Derv6464/Magik/test/board_data/vega/filteredDataInfo.csv

ts | filteredAltitudeAGL | filteredAcceleration
-0.75 | 0.8725128173828125 | 0.009731292724609375
-0.74 | 0.4420928955078125 | 0.009731292724609375
-0.73 | 0.4420928955078125 | 0.019464492797851562
-0.72 | 0.4420928955078125 | 0.019464492797851562
-0.71 | 0.4420928955078125 | 0.019464492797851562
-0.7 | 0.4420928955078125 | 0.019464492797851562
-0.69 | 0.4420928955078125 | 0.019464492797851562
-0.68 | 0.5205535888671875 | 0.019464492797851562
-0.67 | 0.5205535888671875 | 0.019464492797851562
-0.66 | 0.5205535888671875 | 0.019464492797851562
-0.65 | 0.5205535888671875 | 0.019464492797851562
-0.64 | 0.946990966796875 | 0.038928985595703125
-0.63 | 1.18878173828125 | 0.05839347839355469
-0.62 | 1.18878173828125 | 0.0486602783203125
-0.61 | 1.013916015625 | 0.0486602783203125
-0.6 | 1.013916015625 | 0.038928985595703125
-0.59 | 1.013916015625 | 0
-0.58 | 1.013916015625 | -0.009731292724609375
-0.57 | 1.1788177490234375 | -0.009731292724609375
-0.56 | 1.1788177490234375 | 0.0486602783203125
-0.55 | 1.1788177490234375 | 0.0486602783203125
-0.54 | 1.013916015625 | 0.0486602783203125
-0.53 | 1.013916015625 | 0.05839347839355469
-0.52 | 0.3279266357421875 | 0
-0.51 | 1.1788177490234375 | 0
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
