Derv6464/Magik/test/board_data/vega/flightInfo.csv

ts | height | velocity | acceleration
-0.75 | 0.4530242681503296 | 0.1455255150794983 | -0.02075336128473282
-0.74 | 0.4542248249053955 | 0.14505557715892792 | -0.02075744792819023
-0.73 | 0.45539671182632446 | 0.14465756714344025 | -0.011028729379177094
-0.72 | 0.45654067397117615 | 0.1442347764968872 | -0.011033594608306885
-0.71 | 0.4576570689678192 | 0.14378778636455536 | -0.01103883609175682
-0.7 | 0.4587462246417999 | 0.14331720769405365 | -0.011044444516301155
-0.69 | 0.45980846881866455 | 0.14282359182834625 | -0.011050410568714142
-0.68 | 0.46245095133781433 | 0.1439698040485382 | -0.011030841618776321
-0.67 | 0.46505051851272583 | 0.1450599730014801 | -0.01101214811205864
-0.66 | 0.4676075279712677 | 0.14609502255916595 | -0.010994315147399902
-0.65 | 0.4701223075389862 | 0.1470758467912674 | -0.010977329686284065
-0.64 | 0.4813291132450104 | 0.1572326123714447 | 0.008643997833132744
-0.63 | 0.497358500957489 | 0.17246860265731812 | 0.02834136039018631
-0.62 | 0.5132084488868713 | 0.1872667670249939 | 0.01883569173514843
-0.61 | 0.5252976417541504 | 0.19802352786064148 | 0.019000258296728134
-0.6 | 0.5372442007064819 | 0.20842623710632324 | 0.009429508820176125
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
