Derv6464/Magik/test/board_data/vega/flightStates.csv

ts | state
0 | 3
5.69 | 4
21.22 | 5
110.36 | 6
122.12 | 7
