Derv6464/Magik/test/board_data/vega/gnssInfo.csv

ts | latitude | longitude | satellites
-0.58 | 39.39009475708008 | -8.289483070373535 | 12
-0.28 | 39.39009475708008 | -8.289483070373535 | 12
0.02 | 39.39009094238281 | -8.289483070373535 | 12
0.32 | 39.39009094238281 | -8.289483070373535 | 12
0.52 | 39.39009094238281 | -8.289485931396484 | 0
1.72 | 39.39009094238281 | -8.289485931396484 | 0
10.52 | 39.38783264160156 | -8.287121772766113 | 0
10.72 | 39.38783264160156 | -8.287121772766113 | 12
11.22 | 39.38752746582031 | -8.286745071411133 | 9
11.42 | 39.38752746582031 | -8.286745071411133 | 9
11.72 | 39.387413024902344 | -8.28659439086914 | 10
12.02 | 39.387413024902344 | -8.28659439086914 | 6
12.22 | 39.38726043701172 | -8.286388397216797 | 11
12.72 | 39.38726043701172 | -8.286388397216797 | 12
13.22 | 39.38726043701172 | -8.286388397216797 | 7
13.42 | 39.386959075927734 | -8.28598690032959 | 8
13.62 | 39.38691329956055 | -8.285917282104492 | 10
14.02 | 39.38682174682617 | -8.285774230957031 | 10
14.22 | 39.38677215576172 | -8.285700798034668 | 9
14.82 | 39.38661575317383 | -8.28543758392334 | 10
15.02 | 39.38661575317383 | -8.28543758392334 | 8
15.22 | 39.38661575317383 | -8.28543758392334 | 10
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
