Derv6464/Magik/src/outputs/logger.h

#ifndef LOGGER_H
#define LOGGER_H
#include "../config.h"
#include "../drivers/driver_out.h"
#include "../sensors/data.h"

#ifdef LOG_INTERNAL_FLASH
#include "../drivers/flash_internal/flash_internal.h"
#endif

class Logger{
public:
    Logger();
    ~Logger();
    void send(int* data);
    void init();
    void save_settings(flash_internal_data settings);
    flash_internal_data get_settings();


private:
    DriverOut* logger = nullptr;
};

#endif // LOGGER_H
