Derv6464/Magik/src/sensors/data.h

#ifndef DATA_H
#define DATA_H
#include "FreeRTOS.h"
#include "queue.h"
#include <stdio.h>

//12 bytes
struct accle_data
{
    float x{0};
    float y{0};
    float z{0};
};

struct gyro_data
{
    int16_t x{0};
    int16_t y{0};
    int16_t z{0};
};

//10 bytes update
struct baro_data
{
    int32_t pressure{101325};
    float temperature{0};
    float altitude{0};
};

//12 bytes
struct prediction_data
{
    float altitude{0};
    float velocity{0};
    float acceleration{0};
};

//188 bits (no predict) 
struct core_flight_data
{
    uint32_t time{0};
    baro_data barometer;
    accle_data acceleration;
    bool setting_pin{0};
    bool bt_active{0};
};

//25 bytes
struct gps_data
{
    double latitude;
    double longitude;
    float altitude;
    float velocity;
    uint8_t satellites;
};


struct imu_data
{
    accle_data acceleration;
    gyro_data gyro;
    int temperature; //check this
};

//39 bytes
struct secondary_flight_data
{
    uint16_t time;
    gps_data gps;
    accle_data acceleration;
   // imu_data imu;
};

struct flight_data
{
    prediction_data prediction;
    core_flight_data core_data;
    secondary_flight_data secondary_data;
    int state;
};


struct AllQueuesArgs {
    QueueHandle_t coreDataQueue;
    QueueHandle_t secDataQueue;
    QueueHandle_t flightDataQueue;
};

struct flash_internal_data {
    int main_height;
    int drouge_delay;
    int liftoff_thresh;
    int last_log;
};

#endif // DATA_H
