Derv6464/Magik/src/tools/bt_server_gap.h

#include <stdio.h>
#include "btstack.h"


// Flag for general discoverability
#define APP_AD_FLAGS 0x06

// GAP data packet (must not exceed 32 bytes)
static uint8_t adv_data[] = {
    // Flags general discoverable
    0x02, BLUETOOTH_DATA_TYPE_FLAGS, APP_AD_FLAGS,
    // Name
    0x06, BLUETOOTH_DATA_TYPE_COMPLETE_LOCAL_NAME, 'M', 'a', 'g', 'i', 'k',
    // Custom Service UUID
    0x03, BLUETOOTH_DATA_TYPE_COMPLETE_LIST_OF_16_BIT_SERVICE_CLASS_UUIDS, 0x10, 0xFF,
};
static const uint8_t adv_data_len = sizeof(adv_data);

// HCI packet handler
void packet_handler(uint8_t packet_type, uint16_t channel, uint8_t *packet, uint16_t size) {
    UNUSED(size);
    UNUSED(channel);
    bd_addr_t local_addr;
    if (packet_type != HCI_EVENT_PACKET) return;

    // Retrieve event type from HCI packet
    uint8_t event_type = hci_event_packet_get_type(packet);
    printf("Event: %d\n", event_type);
    // Switch on event type . . .
    switch(event_type){
        // Setup GAP advertisement
        case BTSTACK_EVENT_STATE: {
            if (btstack_event_state_get_state(packet) != HCI_STATE_WORKING) return;
            gap_local_bd_addr(local_addr);
            printf("BTstack up and running on %s.\n", bd_addr_to_str(local_addr));
            // setup advertisements
            uint16_t adv_int_min = 800;
            uint16_t adv_int_max = 800;
            uint8_t adv_type = 0;
            bd_addr_t null_addr;
            memset(null_addr, 0, 6);
            gap_advertisements_set_params(adv_int_min, adv_int_max, adv_type, 0, null_addr, 0x07, 0x00);
            assert(adv_data_len <= 31); // ble limitation
            gap_advertisements_set_data(adv_data_len, (uint8_t*) adv_data);
            gap_advertisements_enable(1);

            break;
        }
        // Disconnected from a client
        case HCI_EVENT_DISCONNECTION_COMPLETE:
            printf("Disconnected from client\n");
            break;
        // Ready to send ATT
        case ATT_EVENT_CAN_SEND_NOW:
            break;
        default:
            break;
    }
}
